lhm0/wide-mcu-breadboard/ESP32dev/top_ESP32_900mil_flex2.jpeg

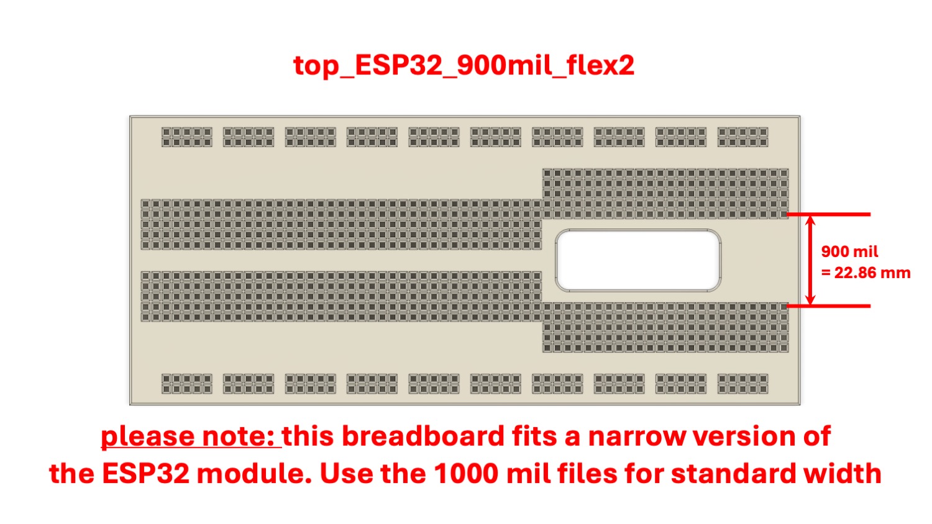
ESP32dev/top_ESP32_900mil_flex2.jpeg
