lhm0/wide-mcu-breadboard/ESP32dev/top_ESP32_1000mil.jpeg

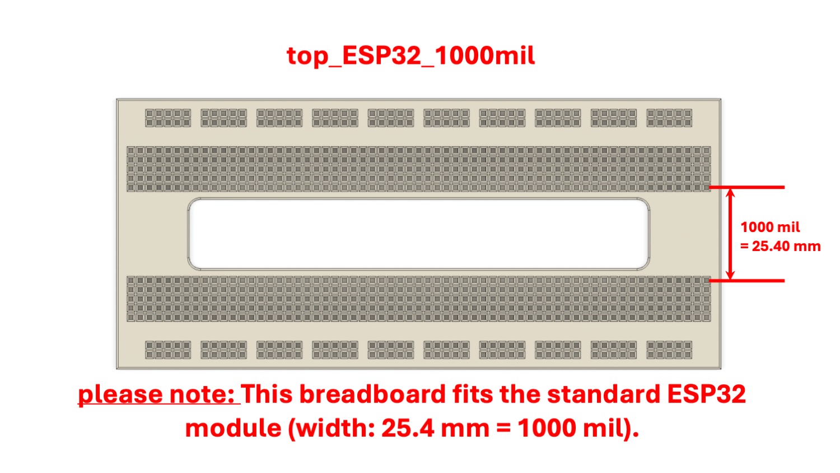
ESP32dev/top_ESP32_1000mil.jpeg
