lhm0/wide-mcu-breadboard/photos/IMG_8470.jpg

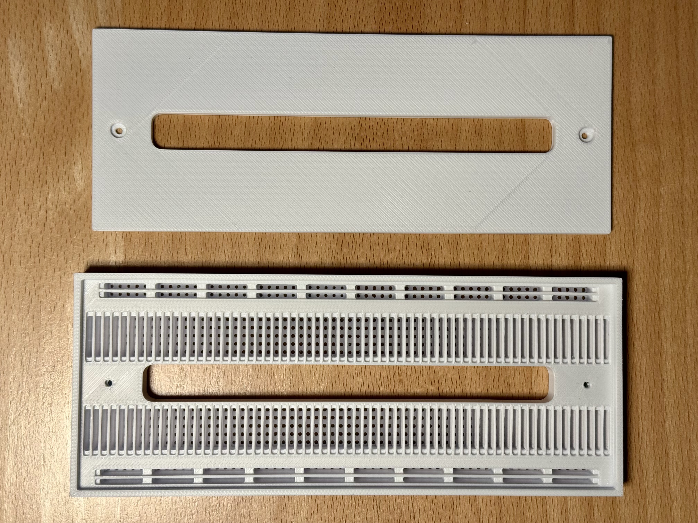
photos/IMG_8470.jpg
