lhm0/wide-mcu-breadboard/photos/IMG_8472.jpg

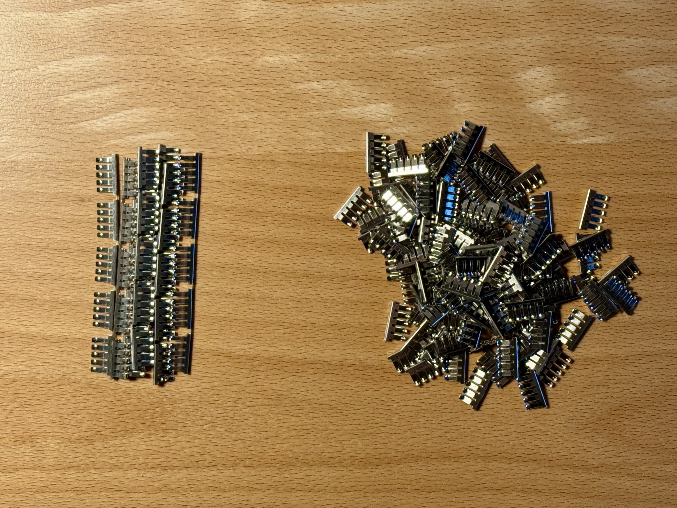
photos/IMG_8472.jpg
