lhm0/wide-mcu-breadboard/photos/IMG_8473.jpg

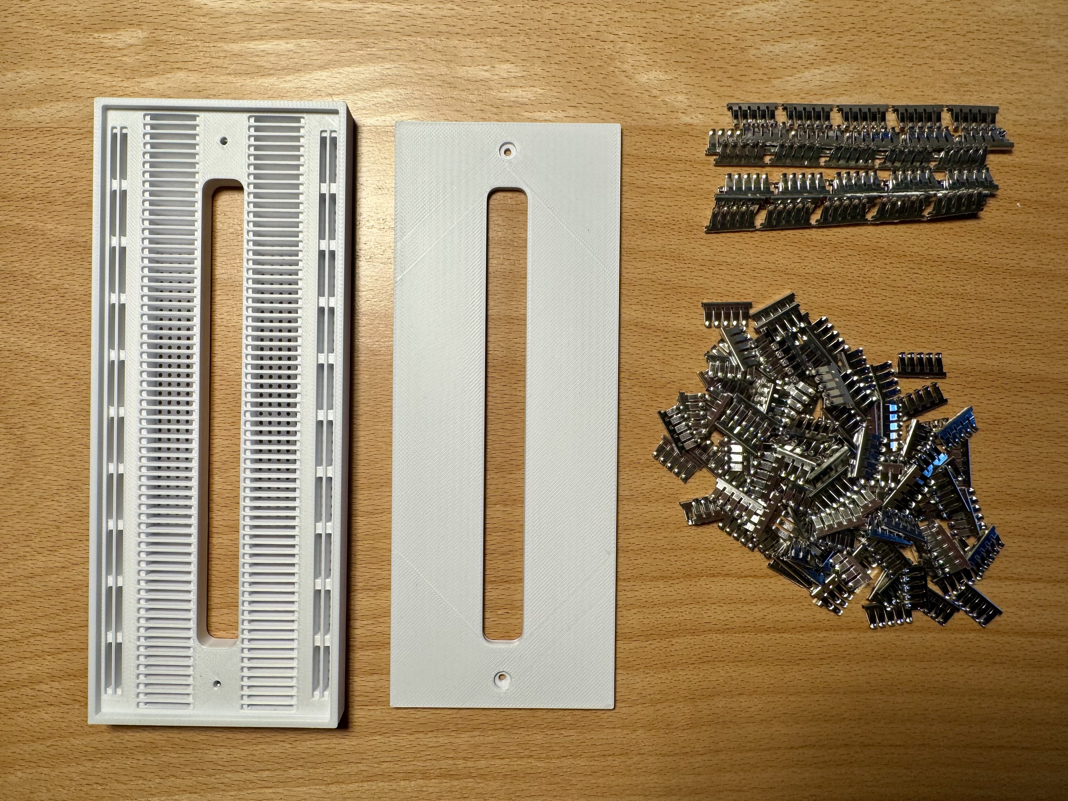
photos/IMG_8473.jpg
