lhm0/wide-mcu-breadboard/photos/IMG_8485.jpg

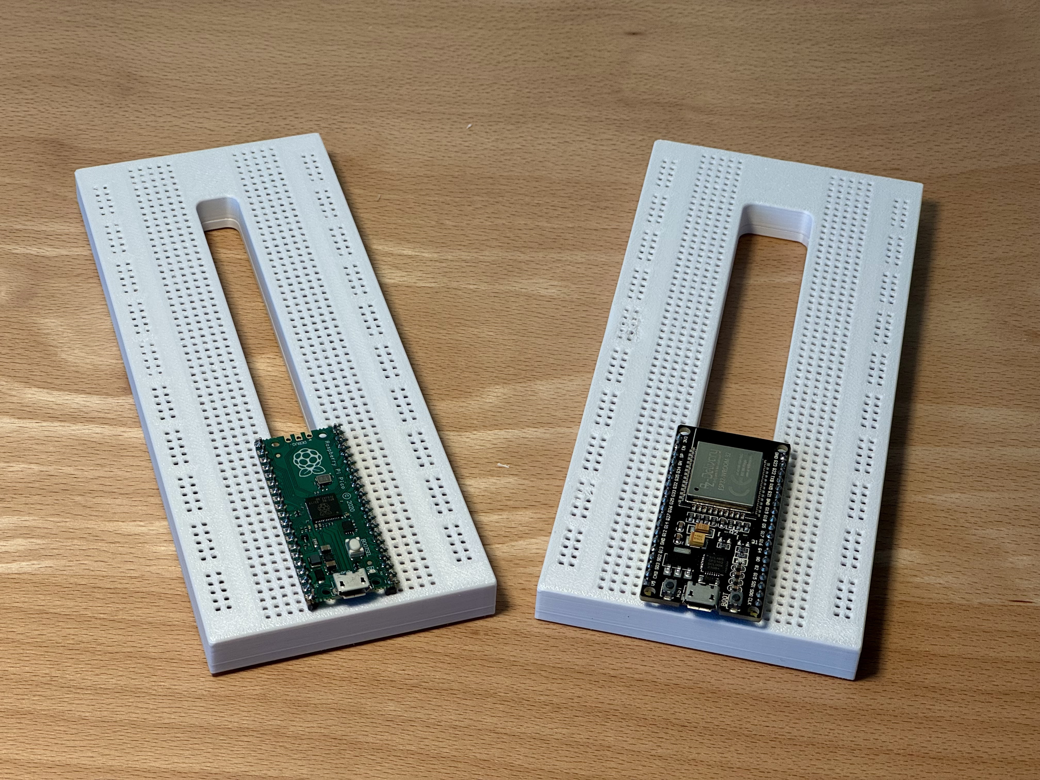
photos/IMG_8485.jpg
