lhm0/wide-mcu-breadboard/photos/IMG_8497.jpg

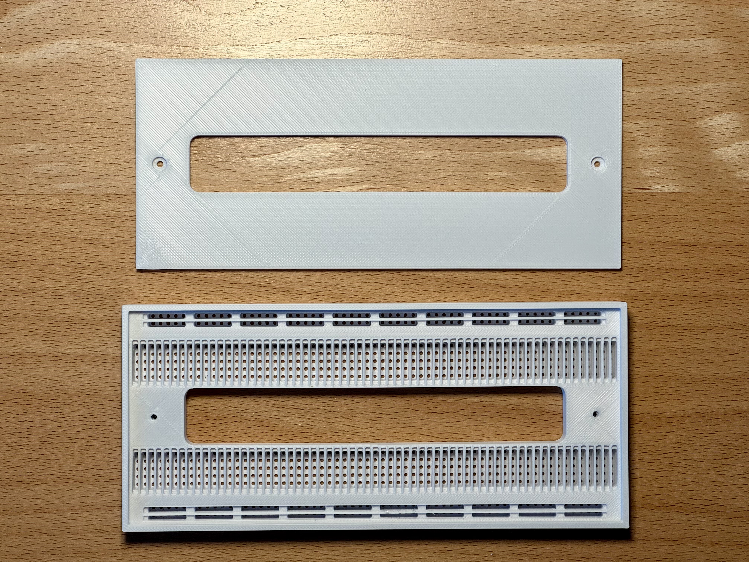
photos/IMG_8497.jpg
