lhm0/wide-mcu-breadboard/photos/IMG_8500.jpg

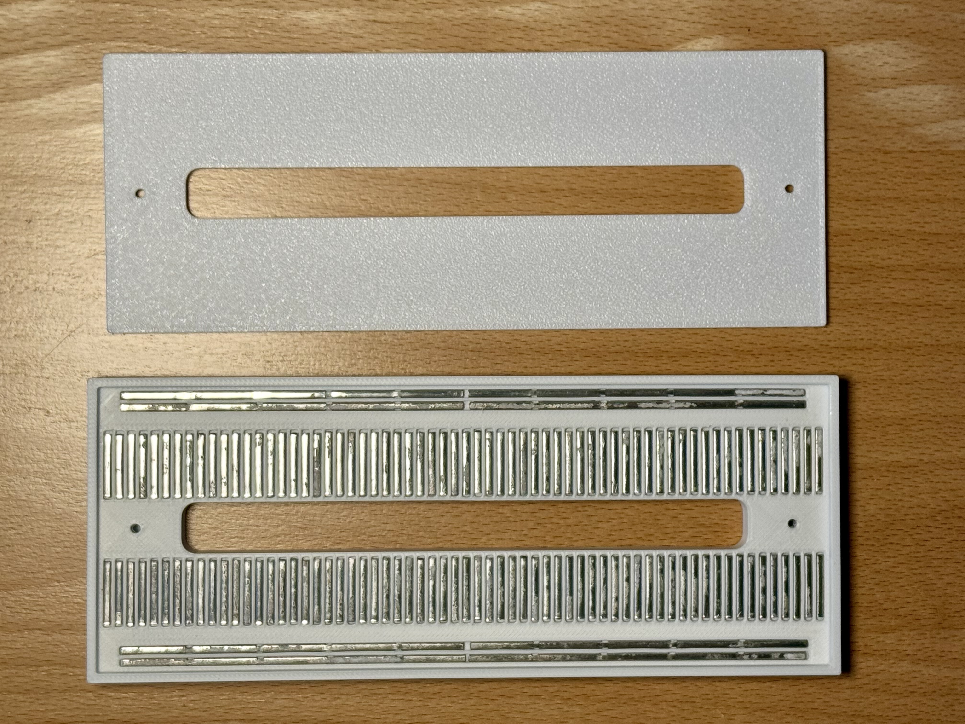
photos/IMG_8500.jpg
