lhm0/wide-mcu-breadboard/photos/IMG_8502.jpg

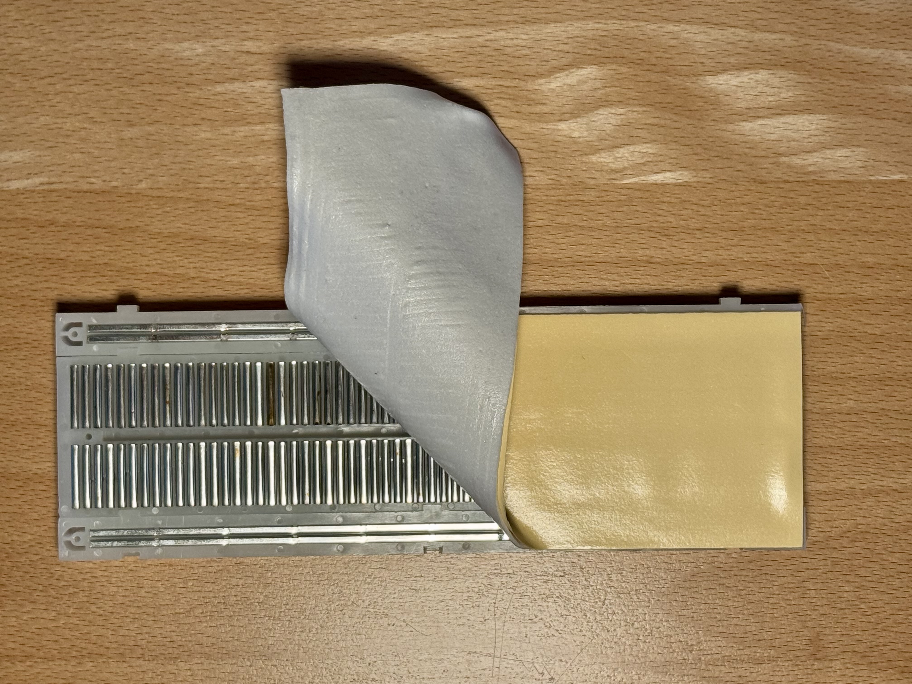
photos/IMG_8502.jpg
