lhm0/wide-mcu-breadboard/photos/IMG_8504.jpg

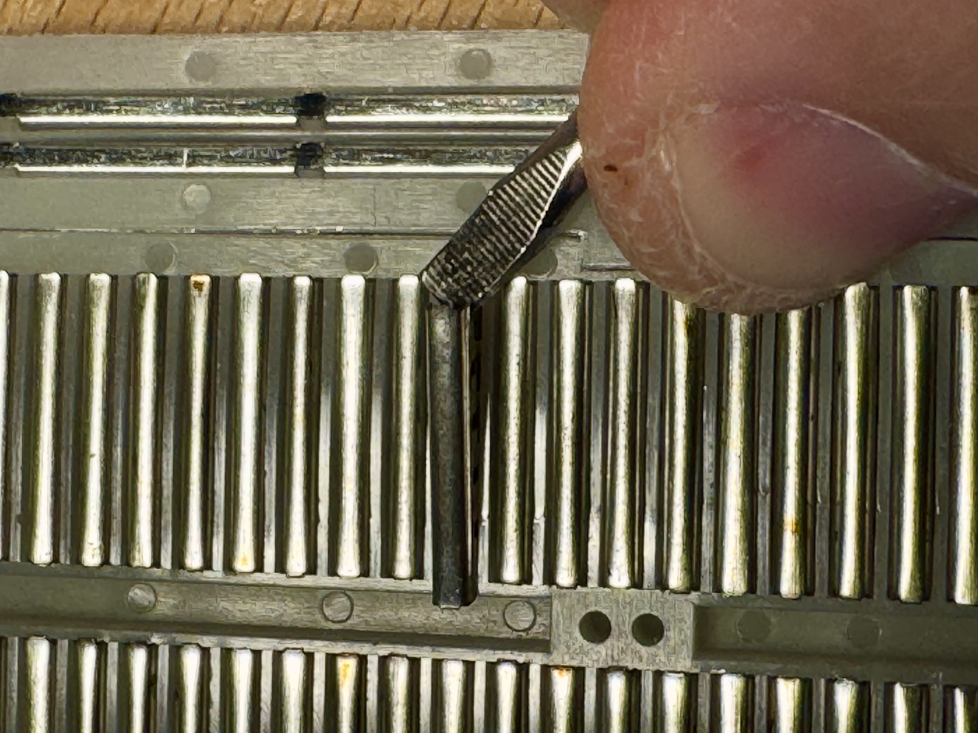
photos/IMG_8504.jpg
