lhm0/wide-mcu-breadboard/photos/IMG_8509.jpg

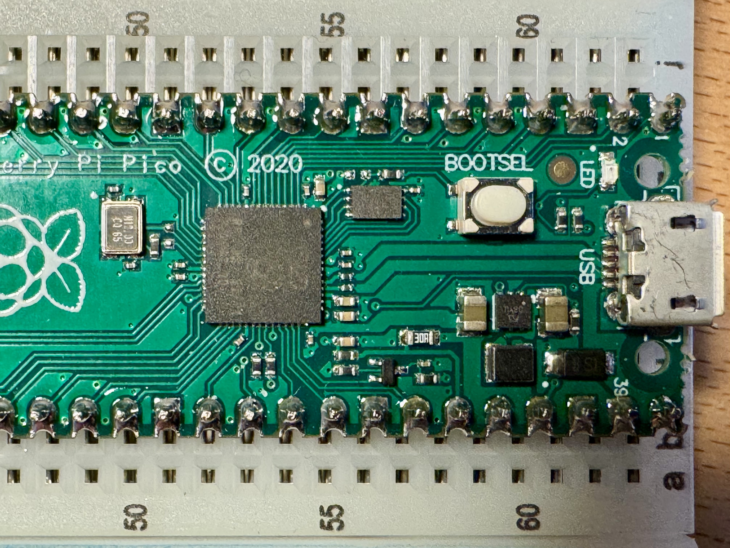
photos/IMG_8509.jpg
