lhm0/wide-mcu-breadboard/photos/IMG_8513.jpg

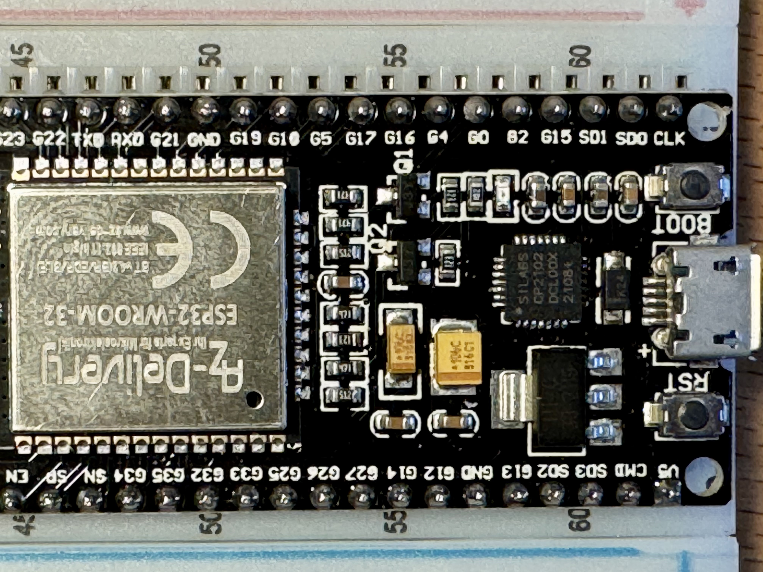
photos/IMG_8513.jpg
