lhm0/wide-mcu-breadboard/photos/IMG_8631.jpg

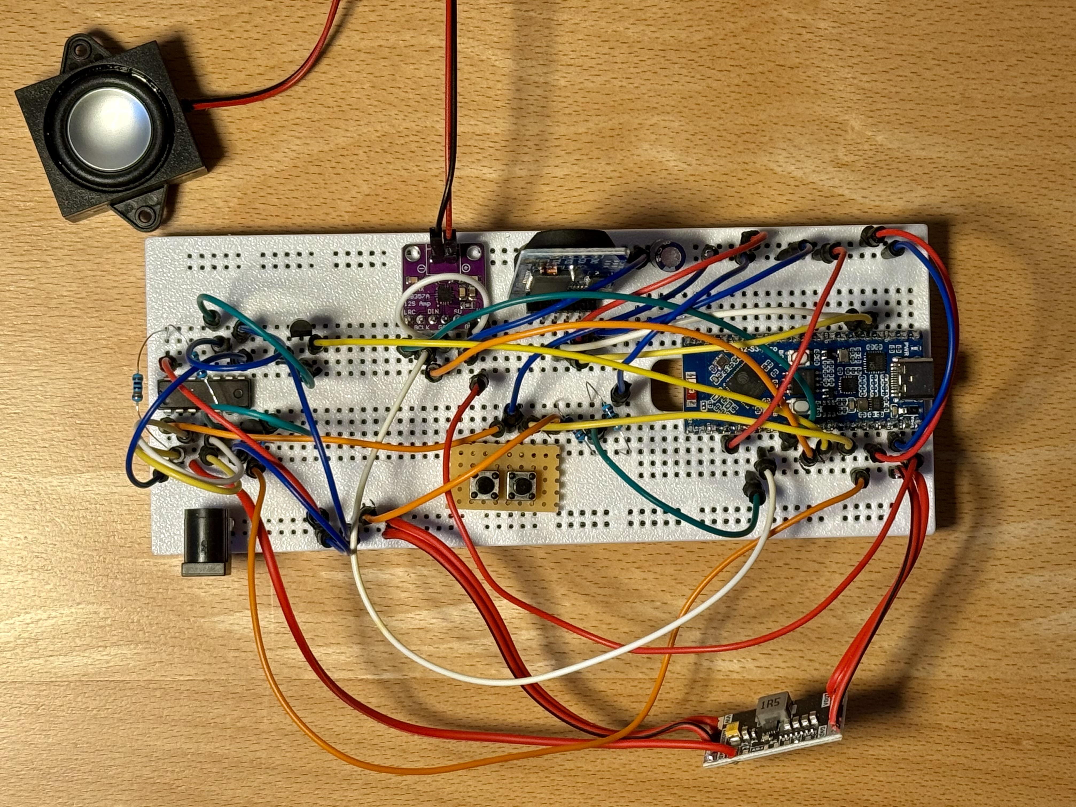
photos/IMG_8631.jpg
