lhm0/wide-mcu-breadboard/photos/IMG_8633.jpeg

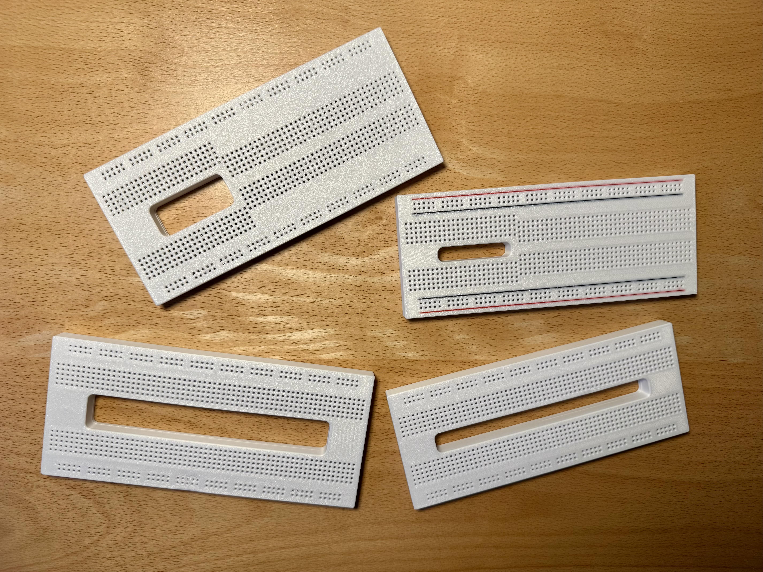
photos/IMG_8633.jpeg
