lhm0/wide-mcu-breadboard/photos/version5.jpeg

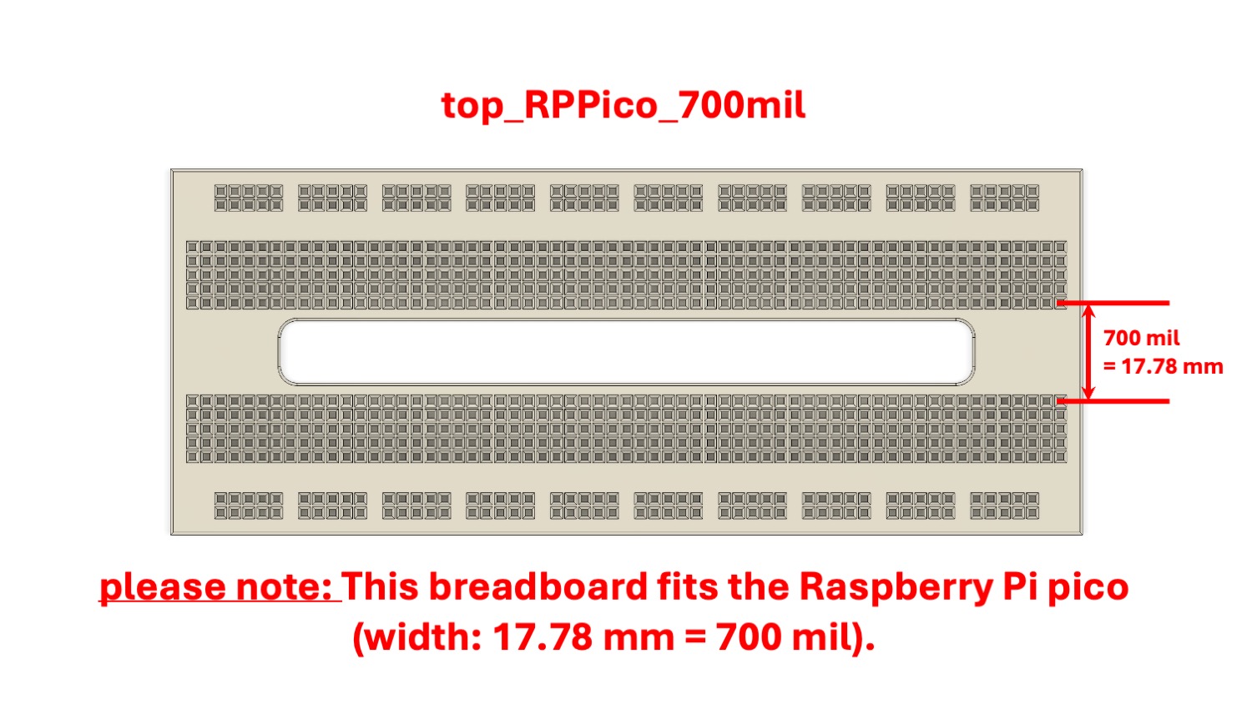
photos/version5.jpeg
