lhm0/wide-mcu-breadboard/photos/version7.jpeg

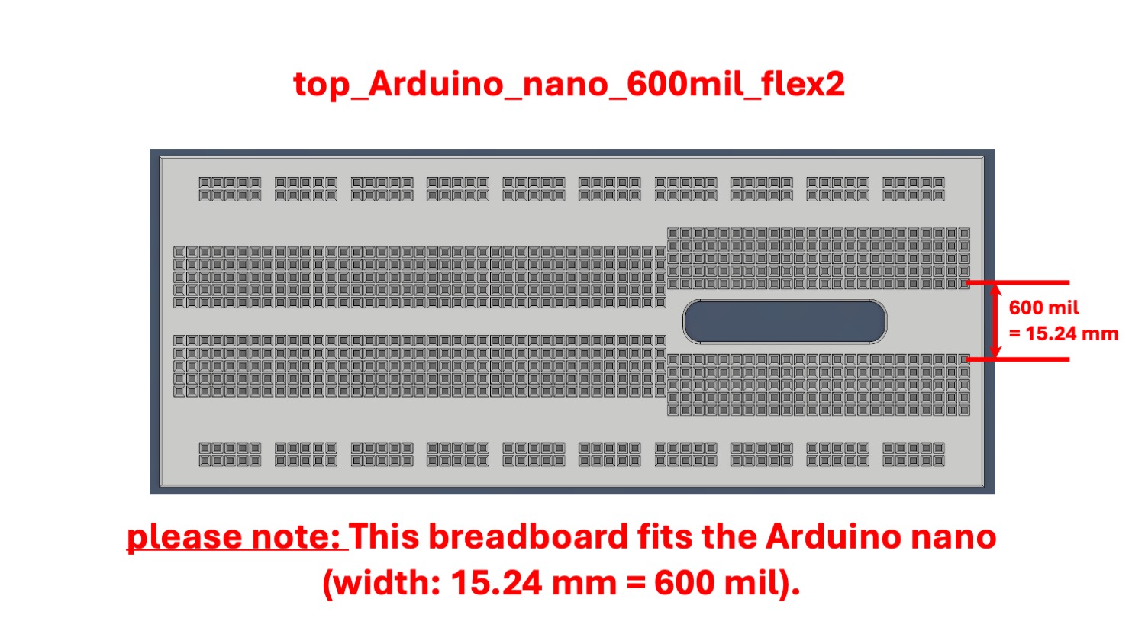
photos/version7.jpeg
