lhm0/wide-mcu-breadboard/ESP32dev/breadboard_ESP32_1000mil.3mf

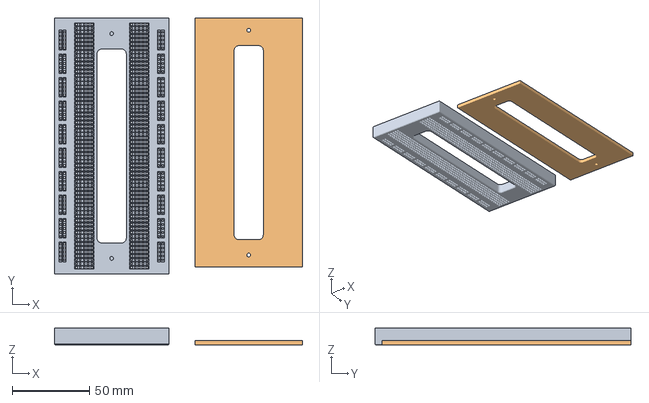
[picture p37: CAD file, 2026-01-19]
ESP32dev/breadboard_ESP32_1000mil.3mf
160.5 x 165.5 x 11.0 mm
top_ESP32dev.stl
bottom_ESP32dev.stl
