lhm0/wide-mcu-breadboard/ESP32dev/bottom_ESP32_1000mil.stl

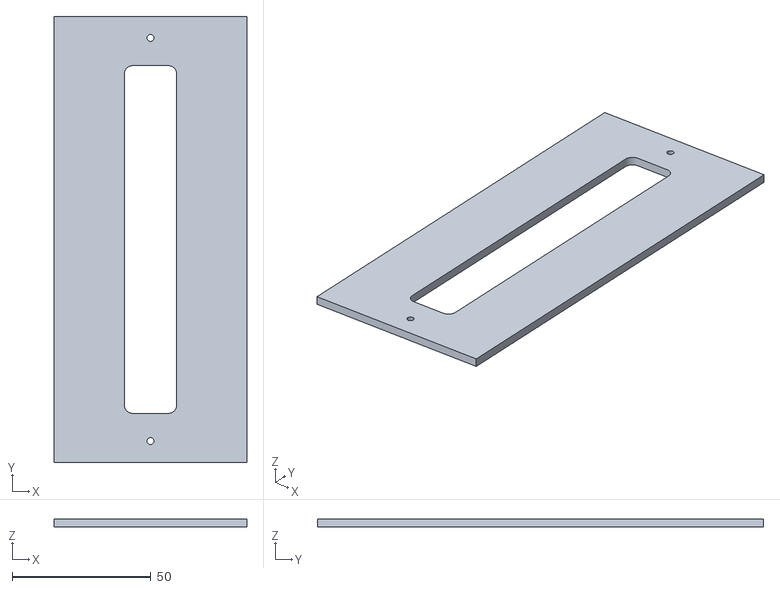
[picture p38: CAD file, 2026-01-19]
ESP32dev/bottom_ESP32_1000mil.stl
69.6 x 161.1 x 3.00
