lhm0/wide-mcu-breadboard/ESP32dev/top_ESP32_1000mil.stl

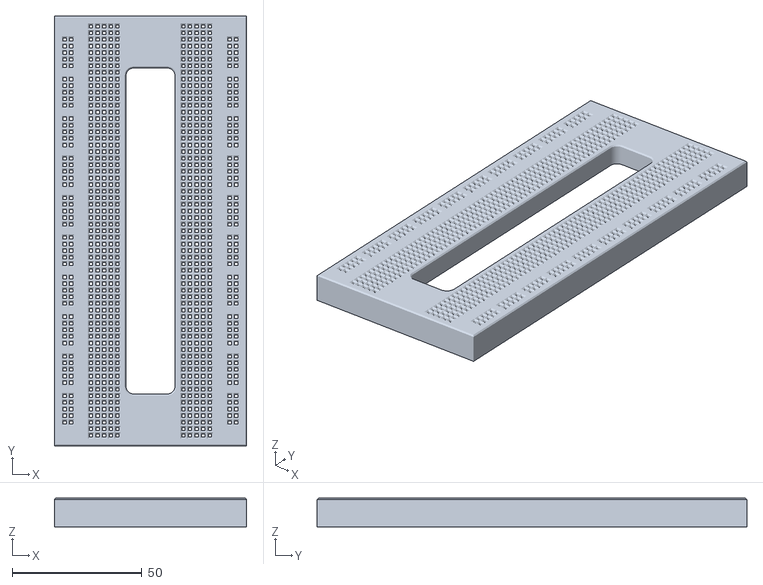
[picture p39: CAD file, 2026-01-19]
ESP32dev/top_ESP32_1000mil.stl
74.0 x 165.5 x 11.0
